jmigal/Monochrome-CRT-Monitor/Schematics/HV Supply/HV Supply.kicad_sch

## KiCad design Schematics/HV Supply/HV Supply.kicad_sch (2026-07-12)

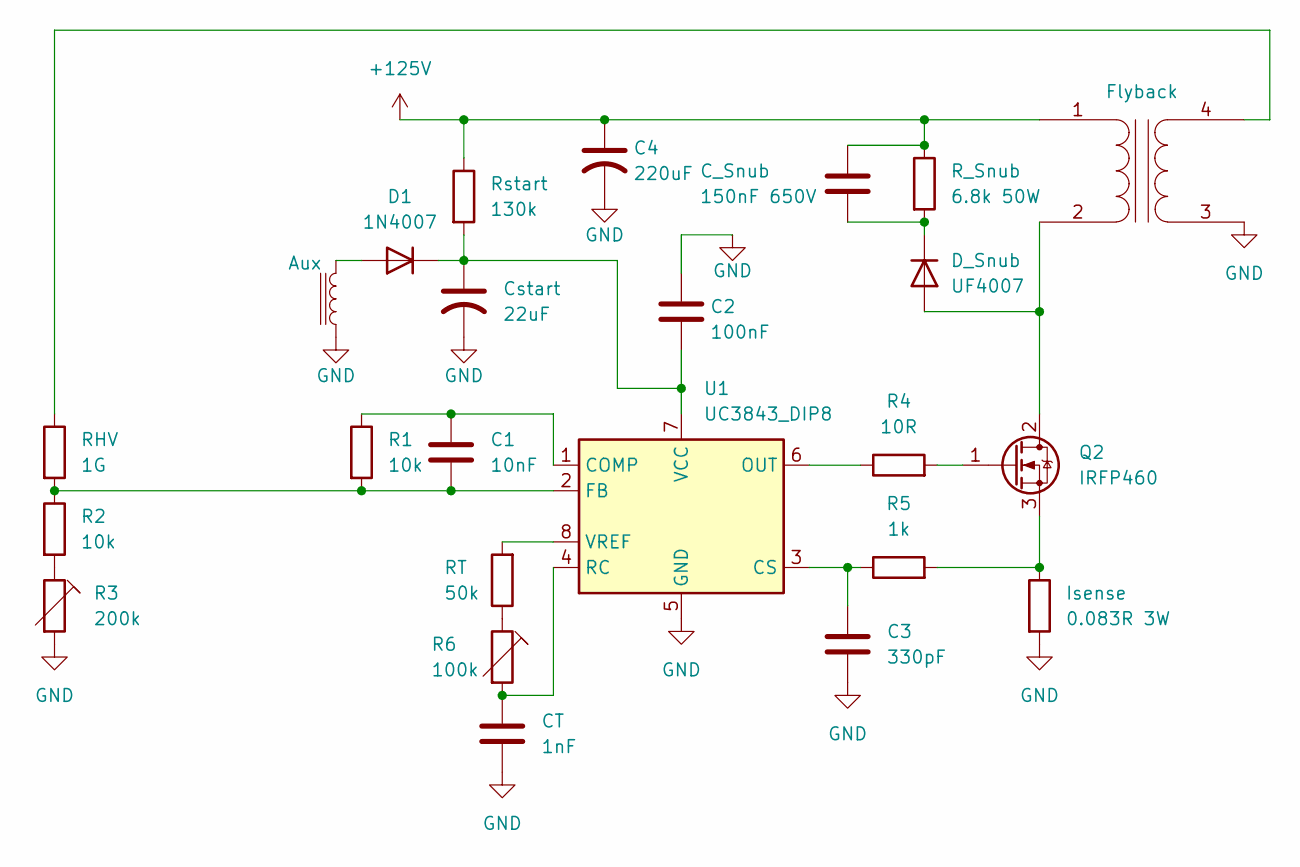
[picture p24: schematic HV Supply.kicad_sch]

Parts:
Aux: (no value)
C1: 10nF
C2: 100nF
C3: 330pF
C4: 220uF
CT: 1nF
C_Snub: 150nF 650V
Cstart: 22uF
D1: 1N4007; D_DO-41_SOD81_P10.16mm_Horizontal
D_Snub: UF4007; D_MELF
Flyback: (no value)
Isense: 0.083R 3W
Q2: IRFP460; TO-247-3_Vertical
R1, R2: 10k
R3: 200k
R4: 10R
R5: 1k
R6: 100k
RHV: 1G
RT: 50k
R_Snub: 6.8k 50W
Rstart: 130k
U1: UC3843_DIP8; DIP-8_W7.62mm

Connections:
+125V: C4.1, C_Snub.1, Flyback.1 (AA), R_Snub.1, Rstart.1
GND: Aux.1, C2.1, C3.2, C4.2, CT.2, Cstart.2, Flyback.3 (SA), Isense.2, R3.2, U1.5 (GND)
unnamed: Aux.2, D1.2 (A)
unnamed: C1.1, R1.1, U1.1 (COMP)
unnamed: C1.2, R1.2, R2.1, RHV.2, U1.2 (FB)
unnamed: C2.2, Cstart.1, D1.1 (K), Rstart.2, U1.7 (VCC)
unnamed: C3.1, R5.1, U1.3 (CS)
unnamed: CT.1, R6.2, U1.4 (RC)
unnamed: C_Snub.2, D_Snub.1 (K), R_Snub.2
unnamed: D_Snub.2 (A), Flyback.2 (AB), Q2.2 (D)
unnamed: Flyback.4 (SB), RHV.1
unnamed: Isense.1, Q2.3 (S), R5.2
unnamed: Q2.1 (G), R4.2
unnamed: R2.2, R3.1
unnamed: R4.1, U1.6 (OUT)
unnamed: R6.1, RT.1
unnamed: RT.2, U1.8 (VREF)
