jmigal/Monochrome-CRT-Monitor/Schematics/Horizontal Deflection/Horizontal Deflection.kicad_sch

## KiCad design Schematics/Horizontal Deflection/Horizontal Deflection.kicad_sch (2026-07-12)

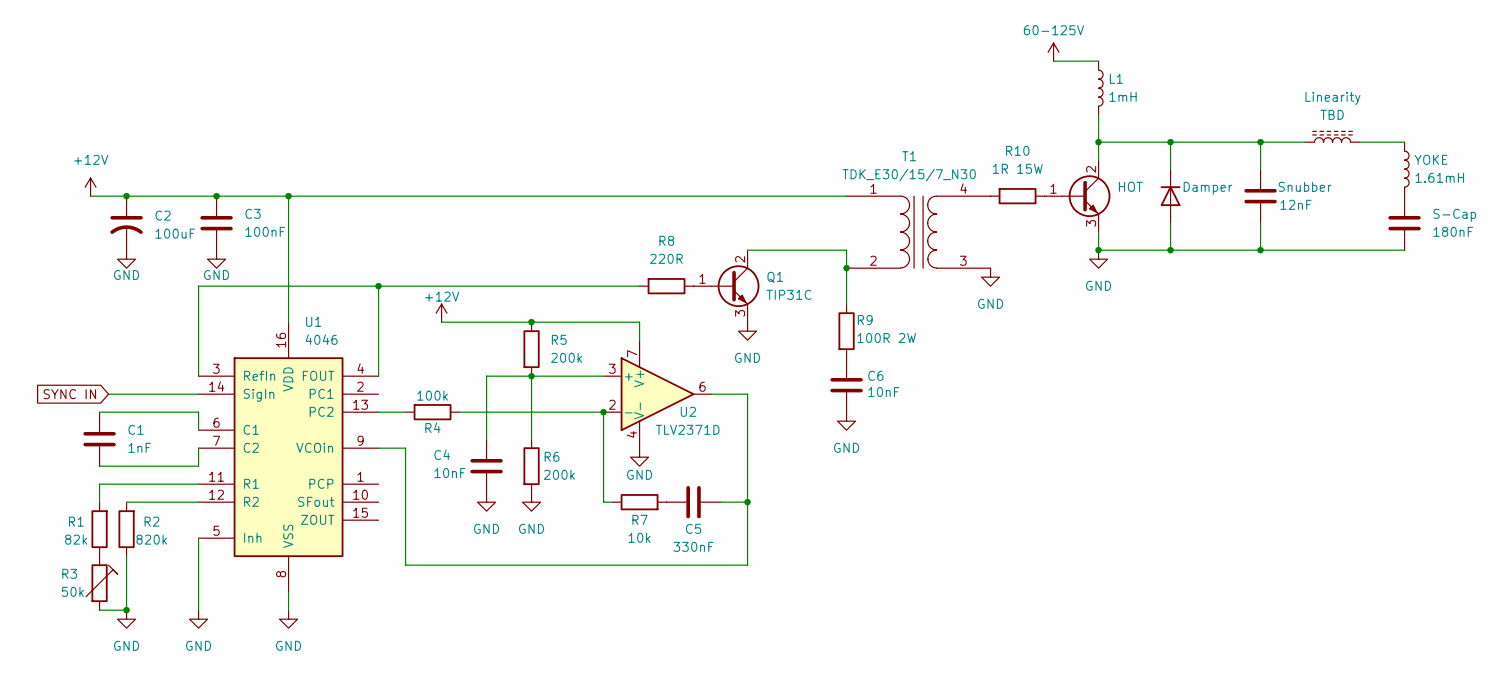
[picture p25: schematic Horizontal Deflection.kicad_sch]

Parts:
C1: 1nF
C2: 100uF
C3: 100nF
C4, C6: 10nF
C5: 330nF
Damper: D_DO-35_SOD27_P7.62mm_Horizontal
HOT: TO-220-3_Vertical
L1: 1mH
Linearity: TBD
Q1: TIP31C; TO-218-3_Vertical
R1: 82k
R2: 820k
R3: 50k
R4: 100k
R5, R6: 200k
R7: 10k
R8: 220R
R9: 100R 2W
R10: 1R 15W
S-Cap: 180nF
Snubber: 12nF
T1: TDK_E30/15/7_N30
U1: 4046
U2: TLV2371D; SOIC-8_3.9x4.9mm_P1.27mm
YOKE: 1.61mH

Connections:
60-125V: L1.1
+12V: C2.1, C3.1, R5.1, T1.1 (AA), U1.16 (VDD), U2.7 (V+)
GND: C2.2, C3.2, C4.2, C6.2, Damper.2 (A), HOT.3 (E), Q1.3 (E), R2.1, R3.2, R6.2, S-Cap.2, Snubber.2, T1.3 (SA), U1.5 (Inh), U1.8 (VSS), U2.4 (V-)
unnamed: C1.1, U1.6 (C1)
unnamed: C1.2, U1.7 (C2)
unnamed: C4.1, R5.2, R6.1, U2.3 (+)
unnamed: C5.1, R7.2
unnamed: C5.2, U1.9 (VCOin), U2.6
unnamed: C6.1, R9.2
unnamed: Damper.1 (K), HOT.2 (C), L1.2, Linearity.1, Snubber.1
unnamed: HOT.1 (B), R10.1
unnamed: Linearity.2, YOKE.1
unnamed: Q1.1 (B), R8.1
unnamed: Q1.2 (C), R9.1, T1.2 (AB)
unnamed: R1.1, R3.1
unnamed: R1.2, U1.11 (R1)
unnamed: R2.2, U1.12 (R2)
unnamed: R4.1, R7.1, U2.2 (-)
unnamed: R4.2, U1.13 (PC2)
unnamed: R8.2, U1.3 (RefIn), U1.4 (FOUT)
unnamed: R10.2, T1.4 (SB)
unnamed: S-Cap.1, YOKE.2
SYNC IN: U1.14 (SigIn)
