jmigal/Monochrome-CRT-Monitor/Schematics/Sync Separator/Sync Separator.kicad_sch

## KiCad design Schematics/Sync Separator/Sync Separator.kicad_sch (2026-07-12)

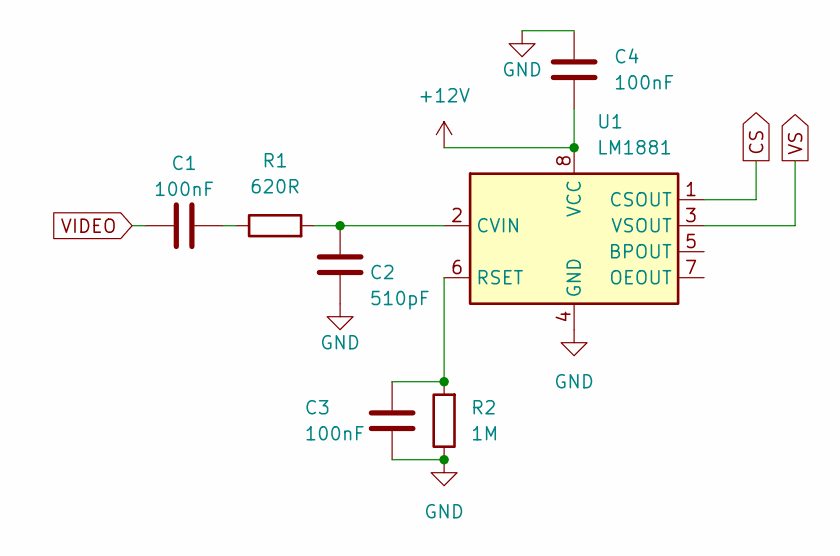
[picture p26: schematic Sync Separator.kicad_sch]

Parts:
C1, C3, C4: 100nF
C2: 510pF
R1: 620R
R2: 1M
U1: LM1881

Connections:
+12V: C4.2, U1.8 (VCC)
CS: U1.1 (CSOUT)
GND: C2.2, C3.2, C4.1, R2.1, U1.4 (GND)
unnamed: C1.2, R1.1
unnamed: C2.1, R1.2, U1.2 (CVIN)
unnamed: C3.1, R2.2, U1.6 (RSET)
VIDEO: C1.1
VS: U1.3 (VSOUT)
