jmigal/Monochrome-CRT-Monitor/Schematics/Vertical Deflection/Vertical Deflection.kicad_sch

## KiCad design Schematics/Vertical Deflection/Vertical Deflection.kicad_sch (2026-07-12)

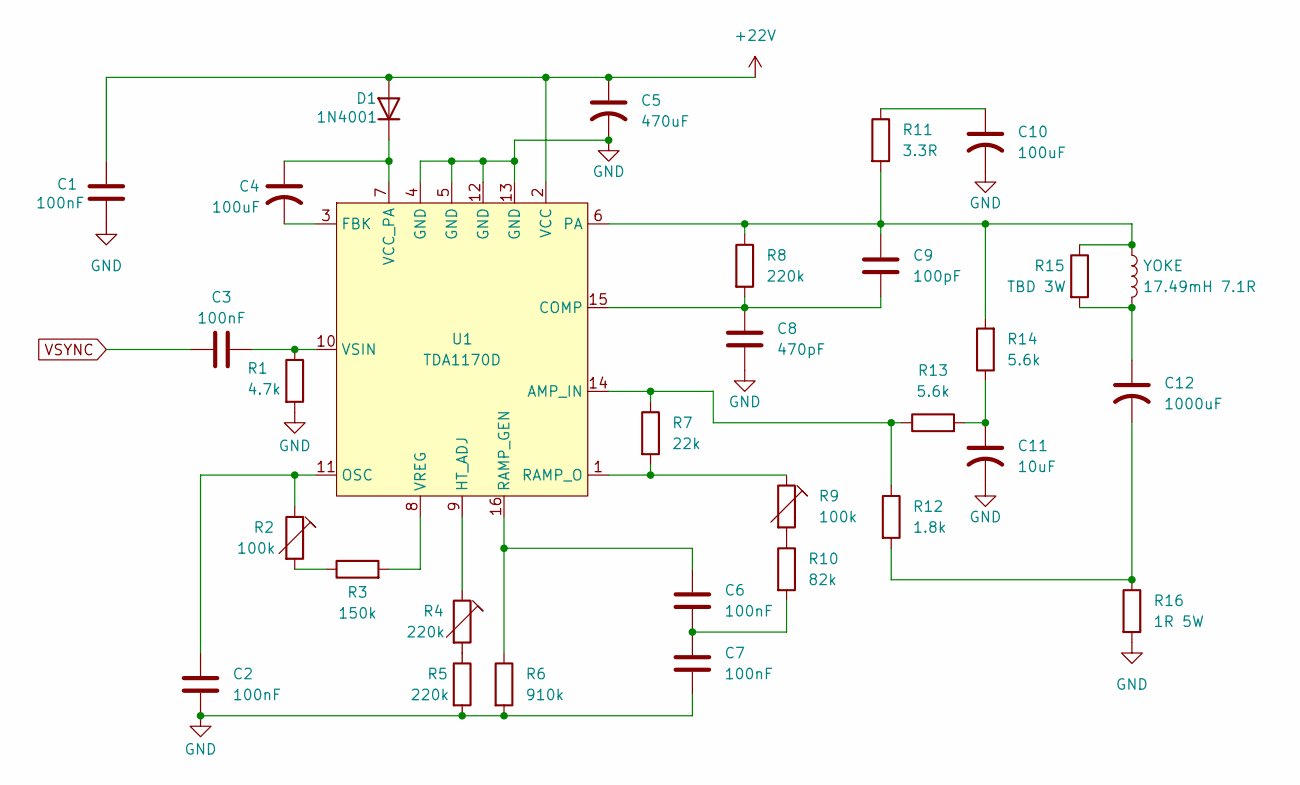
[picture p27: schematic Vertical Deflection.kicad_sch]

Parts:
C1, C2, C3, C6, C7: 100nF
C4, C10: 100uF
C5: 470uF
C8: 470pF
C9: 100pF
C11: 10uF
C12: 1000uF
D1: 1N4001; D_DO-41_SOD81_P10.16mm_Horizontal
R1: 4.7k
R2, R9: 100k
R3: 150k
R4, R5, R8: 220k
R6: 910k
R7: 22k
R10: 82k
R11: 3.3R
R12: 1.8k
R13, R14: 5.6k
R15: TBD 3W
R16: 1R 5W
U1: TDA1170D
YOKE: 17.49mH 7.1R

Connections:
+22V: C1.1, C5.1, D1.2 (A), U1.2 (VCC)
GND: C1.2, C2.2, C5.2, C7.2, C8.2, C10.2, C11.2, R1.2, R5.2, R6.2, R16.2, U1.4 (GND), U1.5 (GND), U1.12 (GND), U1.13 (GND)
unnamed: C2.1, R2.1, U1.11 (OSC)
unnamed: C3.2, R1.1, U1.10 (VSIN)
unnamed: C4.1, D1.1 (K), U1.7 (VCC_PA)
unnamed: C4.2, U1.3 (FBK)
unnamed: C6.1, R6.1, U1.16 (RAMP_GEN)
unnamed: C6.2, C7.1, R10.2
unnamed: C8.1, C9.2, R8.2, U1.15 (COMP)
unnamed: C9.1, R8.1, R11.2, R14.2, R15.1, U1.6 (PA), YOKE.1
unnamed: C10.1, R11.1
unnamed: C11.1, R13.2, R14.1
unnamed: C12.1, R15.2, YOKE.2
unnamed: C12.2, R12.2, R16.1
unnamed: R2.2, R3.1
unnamed: R3.2, U1.8 (VREG)
unnamed: R4.1, U1.9 (HT_ADJ)
unnamed: R4.2, R5.1
unnamed: R7.2, R9.1, U1.1 (RAMP_O)
unnamed: R9.2, R10.1
unnamed: R7.1, R12.1, R13.1, U1.14 (AMP_IN)
VSYNC: C3.1
