jmigal/Monochrome-CRT-Monitor/Schematics/Video Amplifier/Video Amplifier.kicad_sch

## KiCad design Schematics/Video Amplifier/Video Amplifier.kicad_sch (2026-07-12)

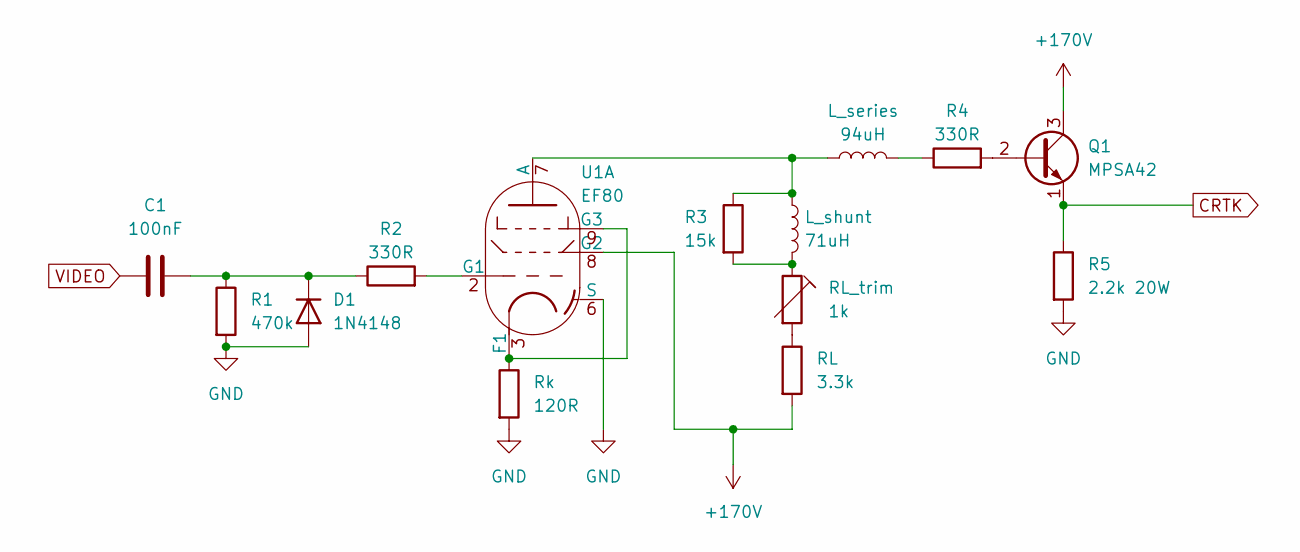
[picture p28: schematic Video Amplifier.kicad_sch]

Parts:
C1: 100nF
D1: 1N4148; D_DO-35_SOD27_P7.62mm_Horizontal
L_series: 94uH
L_shunt: 71uH
Q1: MPSA42; TO-92_Inline
R1: 470k
R2, R4: 330R
R3: 15k
R5: 2.2k 20W
RL: 3.3k
RL_trim: 1k
Rk: 120R
U1: EF80; Valve_Noval_P

Connections:
+170V: Q1.3 (C), RL.2, U1.8 (G2)
CRTK: Q1.1 (E), R5.1
GND: D1.2 (A), R1.2, R5.2, Rk.2, U1.6 (S)
unnamed: C1.2, D1.1 (K), R1.1, R2.1
unnamed: L_series.1, L_shunt.1, R3.1, U1.7 (A)
unnamed: L_series.2, R4.1
unnamed: L_shunt.2, R3.2, RL_trim.1
unnamed: Q1.2 (B), R4.2
unnamed: R2.2, U1.2 (G1)
unnamed: RL.1, RL_trim.2
unnamed: Rk.1, U1.3 (F1), U1.9 (G3)
VIDEO: C1.1
